snowpuppy/augreality/doc/Team5FinalPresentation.pptx

## ECE 477 Final Presentation Team 05 - Fall 2013

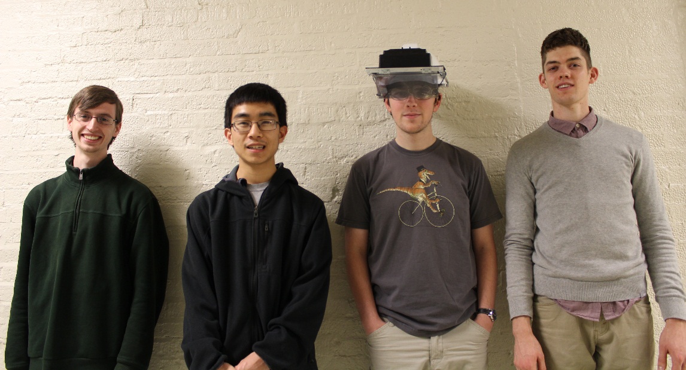
[picture p90: figure]

From left: Thor Smith, Stephen Carlson, Steven Ellis, Alec Green

## Outline

- Project overview
- Block diagram
- Design challenges
- Individual contributions
- Project demonstration
- Questions / discussion

## Project Overview

- Augmented Reality Simulator
  - Play as Pacman in a mobile, outdoor environment.
  - Designed to support other simulations that require an augmented environment and multiple users.
- Contains two primary parts: a headset and a central control unit (CCU)
  - The headset is worn by the user and overlays images of game objects on the user’s view of the environment
  - The CCU remains stationary and communicates information to the headset about simulation logic.

## Slide 4

## Design Challenges

- Packaging
  - Needs to be lightweight and comfortable
  - Stability of IMU mounting
  - Semi-transparent display
- Headset Pi Software
  - 3D rendering
  - SPI communication with µC

## Design Challenges

- Hardware Design
  - PCB needs to fit Raspberry Pi footprint
  - Battery power and power supply
- Headset µC Software
  - XBee communication
  - Sensor filtering
  - SPI communication with Raspberry Pi

## Individual Contributions

- Team Leader - Thor Smith
- Team Member 2 - Alec Green
- Team Member 3 - Stephen Carlson
- Team Member 4 - Steven Ellis

## Team Leader - Thor Smith

- User interface on the Central Control Unit.
- Networking packets sent between the Central Control Unit and the Headset.
- Inter-process Communication between user interface, simulation, and packet program.
- Worked with Steven Ellis on packaging design and construction.
- Organized most team meetings and purchased most parts for project.

## Member 2 - Alec Green

- Google Maps parsing for automatic map generation
  - Image process map tiles
  - GPS location from pixel coordinate
- Packet protocol definition
- IMU sensors
  - Calculate Euler angles from sensor readings
  - Research and design filters
- Compiled Video

## Member 3 - Stephen Carlson

- Design Constraint Analysis
  - Research parts
  - Select candidate based on project requirements
- Schematic and Theory of Operation
  - Power supply design
  - Select pins/ports on microcontroller
- PCB Layout
  - Design for manufacturability
  - Power handling and impedance matching
- Assembly and Soldering

## Member 4 - Steven Ellis

- Graphics
  - Created game 3D models
  - Custom configuration file format
  - OpenGL code
- Raspberry Pi SPI code
  - Integration with graphics
- Packaging
  - Assembly
  - Optics research
  - Model for 3D printed enclosure

## Project Demonstration

1. An ability to render graphics based on the orientation of the user’s head.
2. An ability to render graphics based on the user’s current geospatial location.
3. An ability to monitor and display the battery power level of the headset to the user.
4. An ability to monitor and display the status and quality of the wireless connection to the central control unit.
5. An ability to load headset graphics for a new simulation without re-flashing software on the headset’s microcontroller.

## Questions / Discussion
