snowpuppy/augreality/doc/TCSP9.pptx

## Team 5 environmental impact analysis

Steven Ellis

## Manufacture (very bad)

- Packaging
  - Aluminum, ABS, and acrylic
- Lithium polymer battery
  - LiCoO2 electrode
    - LiFePO4 would be less harmful
- PCB
  - Etching uses either ammonium persulfate
  - Lead solder
    - Switch to lead-free solder
- LCD
  - Sulfur hexafluoride used in manufacture
  - LED backlighting avoids mercury found in CCFL

## Use (not so bad)

- Electricity used to power device
  - Only draws ~5 watts in use
  - ‘Phantom power’ when turned off is tens of microwatts
- Product lifespan
  - Battery lasts ~400 charge cycles
    - LiFePO4 would increase this to ~2000
  - Battery can be replaced without replacing entire unit

## End of life (also pretty bad)

- Packaging
  - Aluminum and plastics can both be recycled
- Lithium polymer battery
  - Nonhazardous waste
  - Can be recycled
- PCB
  - Neither biodegradable nor recyclable
- LCD
  - Neither biodegradable nor recyclable

## Questions?
