snowpuppy/augreality/doc/Team5PCBNarrative.pptx

## PCB Layout Narrative

Team 05 Augmented Reality Project
TCSP #05
Stephen Carlson, Steven Ellis, Alec Stephen Green, Thor Smith

## Abstract

- We propose an augmented reality simulator
  - Allows at least one user to play an electronic game in a mobile, outdoor environment
  - Intended for gaming and other simulations that require an augmented environment
- Contains two primary parts: a headset and a central control unit (CCU)
  - The headset is worn by the user and overlays images of game objects on the user’s view of the environment
  - The CCU remains stationary and communicates information to the headset about simulation logic.

Team 05: Augmented Reality

## Functional Block Diagram


* CCU will not have a PCB

## PSSC Review

- An ability to render graphics based on the orientation of the user’s head.
- An ability to render graphics based on the user’s current geospatial location.
- An ability to monitor and display the battery power level of the headset to the user.
- An ability to monitor and display the status and quality of the wireless connection to the central control unit.
- An ability to load headset graphics for a new simulation without re-flashing software on the headset’s microcontroller.

## Layout Considerations – General

- Advanced Circuits/4PCB specs
  - 5mil trace/5mil space
  - 10mil minimum hole size and 5mil tolerance
- For manufacturability
  - 10mil trace/8mil space
  - 15mil minimum hole size
- No acute angles
- Two layers

## Layout Considerations – MCU

- Oscillator and USB lines match impedance
  - Trace lengths must match
  - No right angles
- Decoupling, oscillator must be adjacent
  - Place some capacitors underneath chip
- Pin locations determine routing success

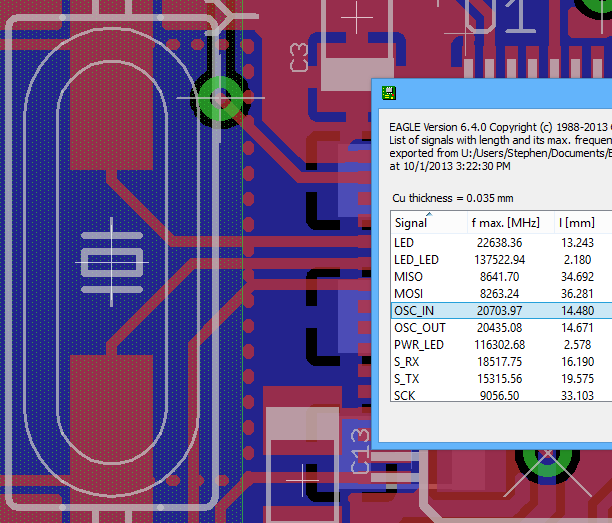
[picture p122: figure]

## Layout Considerations – Power

- Total current could be up to 2A
  - Use low resistance copper pours
  - Multiple large vias for transfer between layers
  - Power from multiple directions (“islands”)
  - Bulk capacitors near regulator, bypass near loads


## Layout Considerations – Other

- Connectors
  - Raspberry PI connector must match motherboard
  - Other connectors must be on edges
- Route I²C, UART, SPI lines together
  - Test points
- Debug LEDs, spare I/O headers
- Place V_ADC regulator near IMU
  - Reduce interference pickup
  - Place XBee far away


## Layout, Full Board

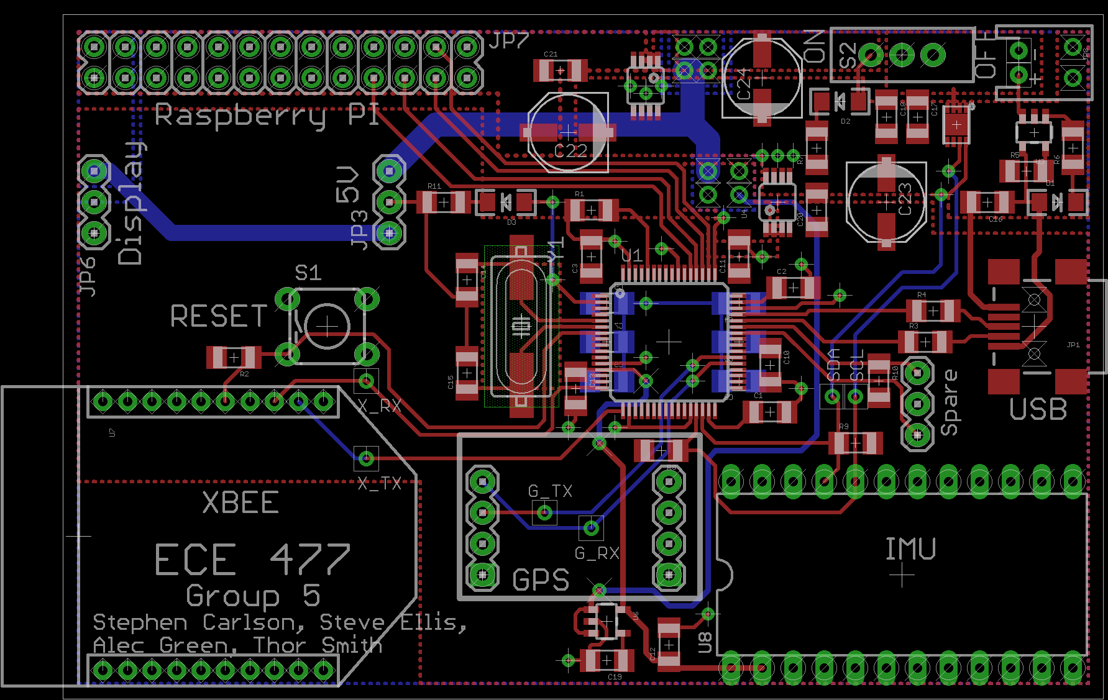
[picture p123: figure]

## Questions

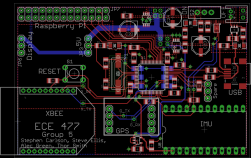
[picture p124: figure]
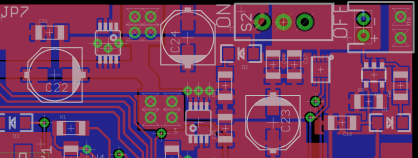
[picture p125: figure]
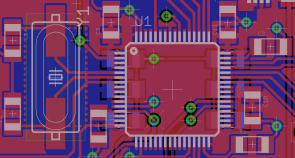
[picture p126: figure]
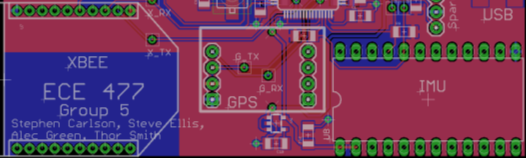
[picture p127: figure]

## Layout, Power Supply

Power Switch

JST Connector

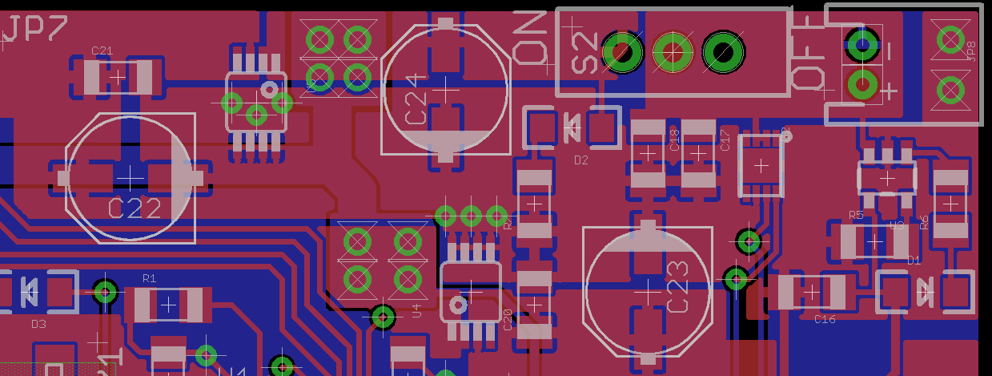
[picture p128: figure]

Core Supply

Fuel Gauge

Power LED

Charger

MCU Supply

Charging LED


## Layout, Microcontroller

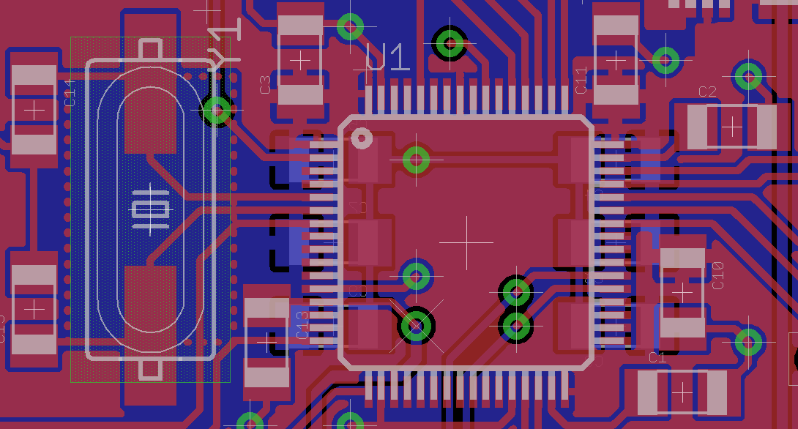
[picture p129: figure]

SPI to
Raspberry PI

8MHz
Oscillator

STM32F4
Microcontroller

To USB
(programming)

To Reset Button

UART to XBee

UART to GPS

I²C to IMU


## Layout, Peripherals

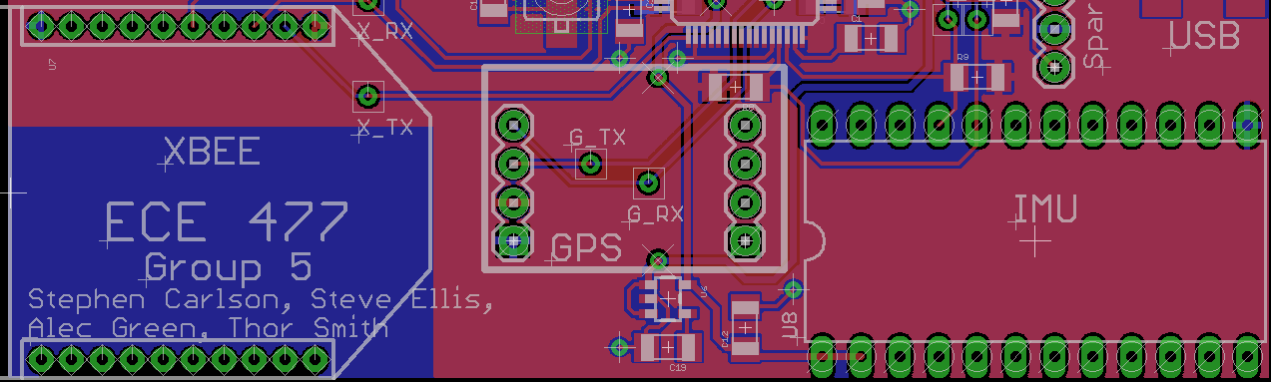
[picture p130: figure]

XBee Pro 900

Venus GPS Breakout

ST 9-DOF IMU Breakout

V_ADC
Supply
