snowpuppy/augreality/doc/FinalSubmission/README - Augmented Reality Simulator.docx

Augmented Reality Final Submission Index File

The Augmented Reality Simulator archive contains the following files, to be reviewed in the order listed.

1. Cornell Cup Final Report : Word document containing final report
2. Graphical Timeline Appendix: Word document containing a visual representation of the timeline
3. Timeline Appendix: Excel spreadsheet containing a listing of dates for the timeline
4. Bill Of Materials Appendix: Excel spreadsheet listing items bought and used for the project
5. First Design Review: PDF file documenting how our presentation was evaluated and comments suggested
6. Second Design Review: Word document explaining main talking points of the design review
7. Phase 1 Senior Design Report: Word document containing the report written for phase 1 of this project
8. Phase 2 Sensor Schematic Appendix: Schematic of phase 2’s sensors and microcontroller system
9. Phase 2 Power Schematic Appendix: Schematic of phase 2’s power supply
10. Phase 2 Sensor PCB Layout Appendix: Printed circuit board (PCB) layout views of phase 2’s sensor and microcontroller PCB
11. Phase 2 Power PCB Layout Appendix: PCB layout views of phase 2’s power supply PCB
12. Phase 1 Schematic Appendix: Schematic of the full system board used for phase 1
13. Phase 1 PCB Layout Appendix: PCB layout views of the full system board used for phase 1
