snowpuppy/augreality/doc/Phase 2 Power PCB Layout.docx

# Layout, Composite

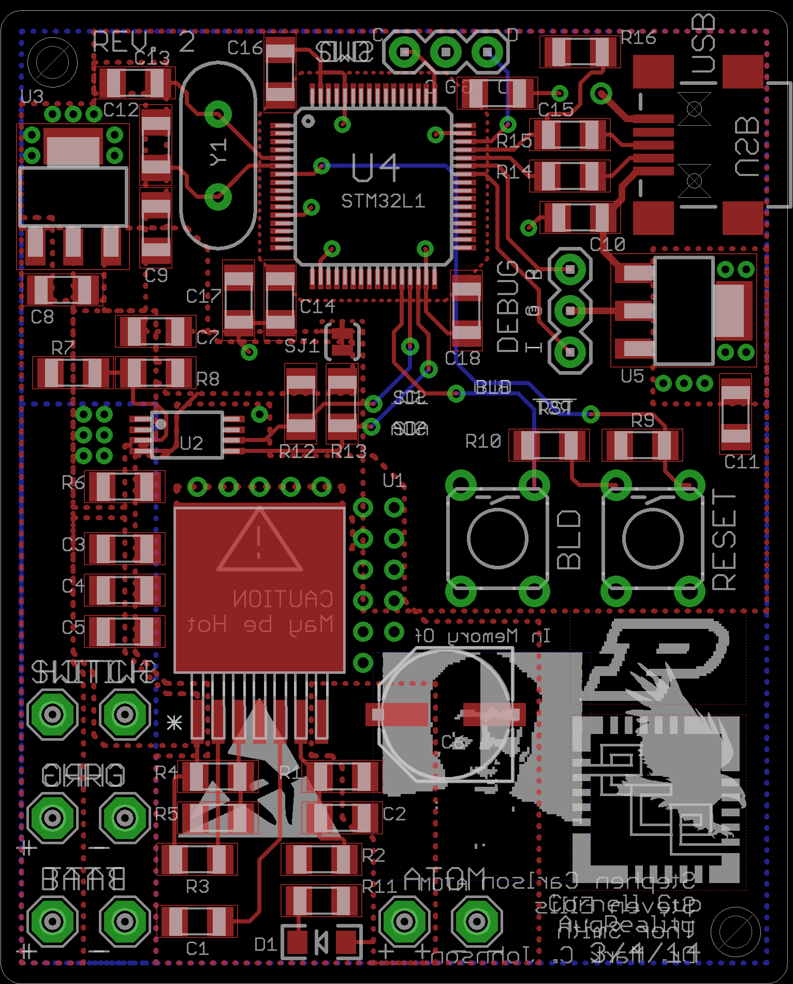
[picture p137: figure]

# Layout, Top Copper

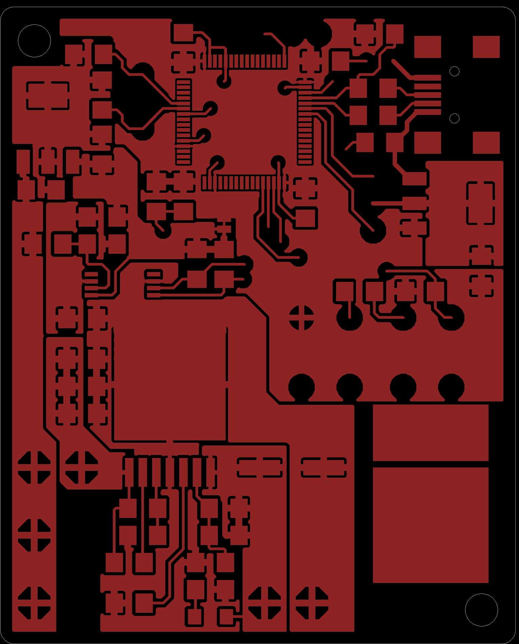
[picture p138: figure]

# Layout, Bottom Copper

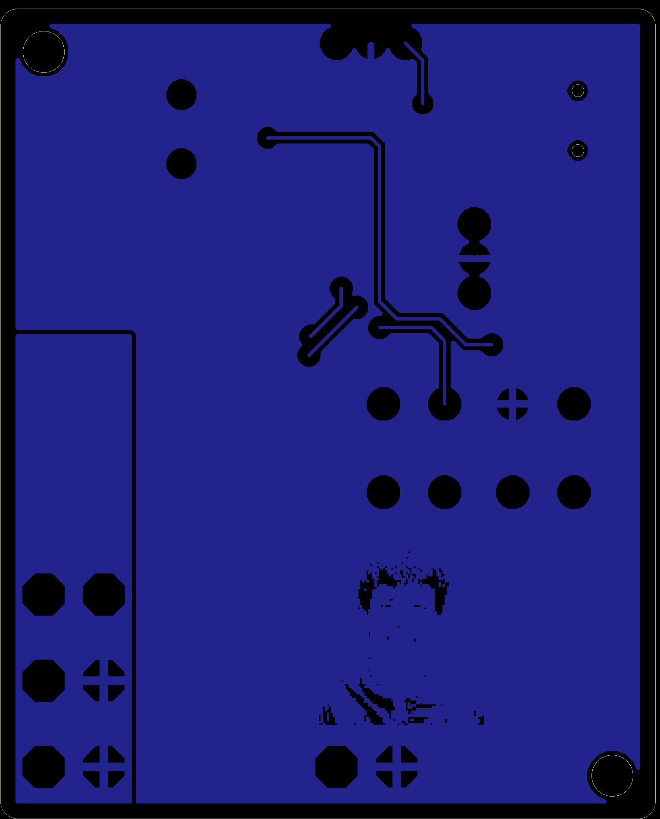
[picture p139: figure]

# Layout, Top Silk Screen

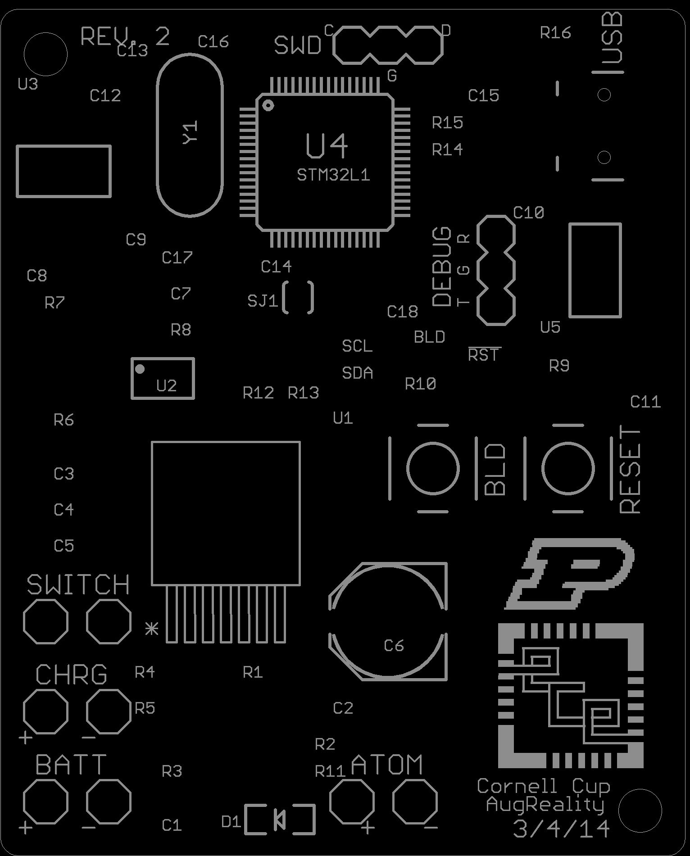
[picture p140: figure]

# Layout, Bottom Silk Screen

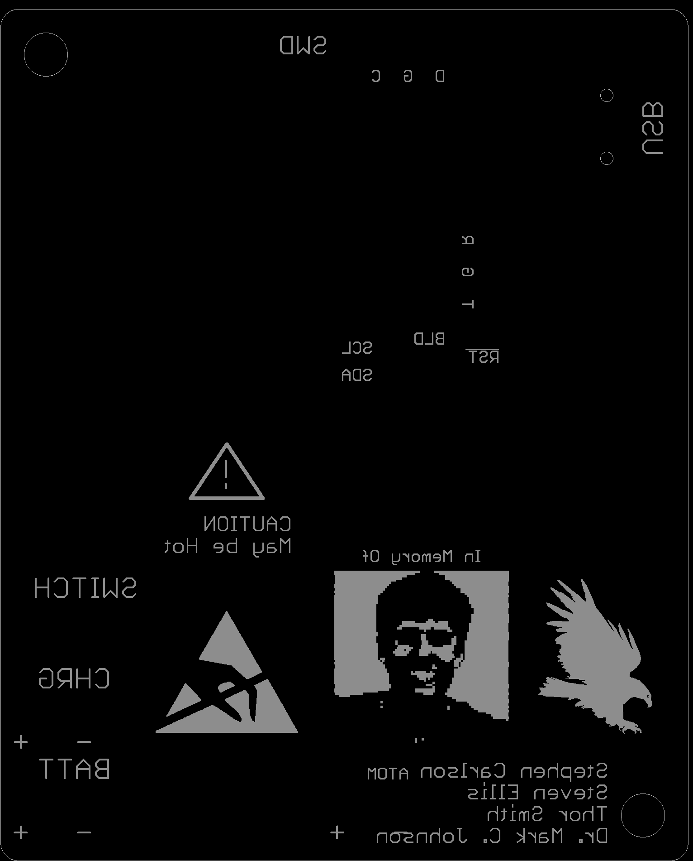
[picture p141: figure]
