snowpuppy/augreality/doc/Phase 2 Sensor PCB Layout.docx

# Layout, Composite

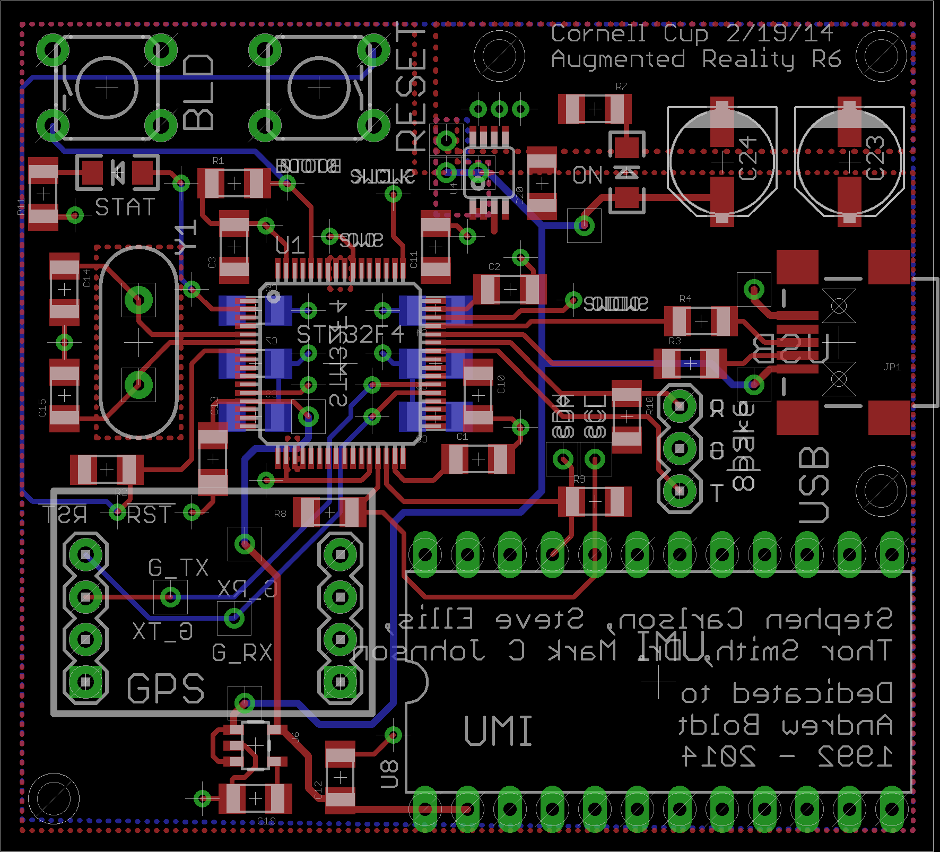
[picture p142: figure]

# Layout, Top Copper

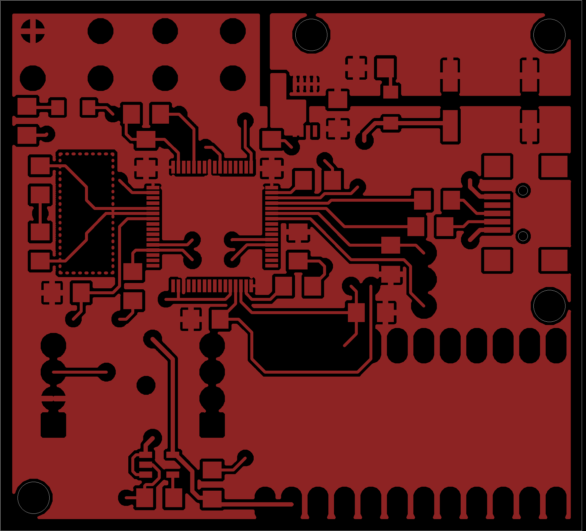
[picture p143: figure]

# Layout, Bottom Copper

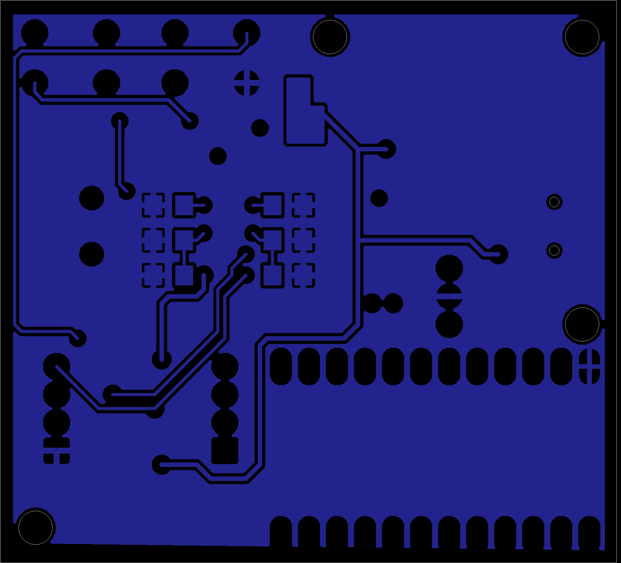
[picture p144: figure]

# Layout, Top Silk Screen

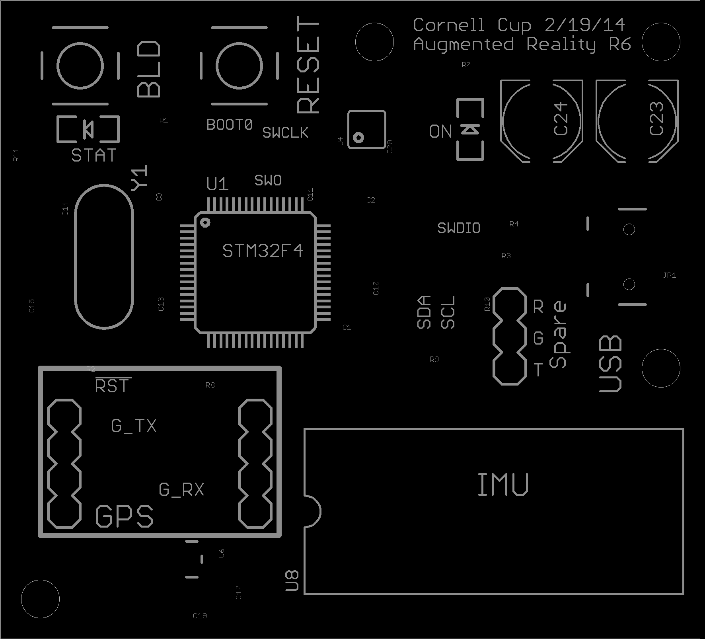
[picture p145: figure]

# Layout, Bottom Silk Screen

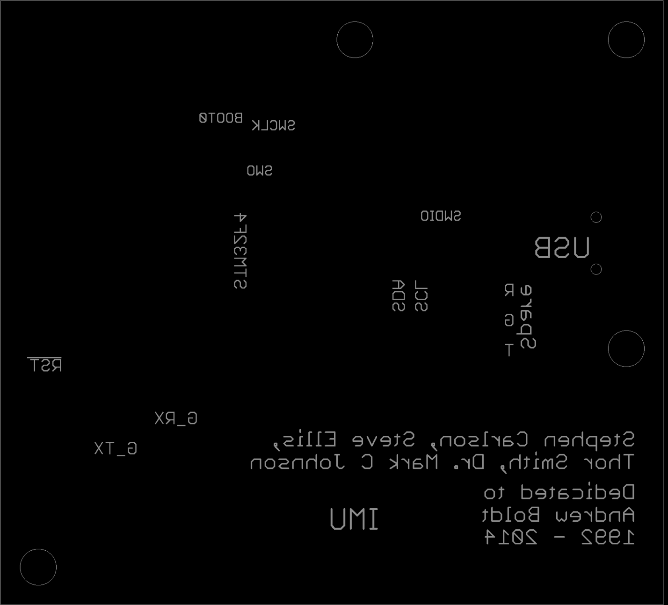
[picture p146: figure]
