snowpuppy/augreality/doc/FinalSubmission/Graphical Timeline Appendix.docx

Graphical Timeline

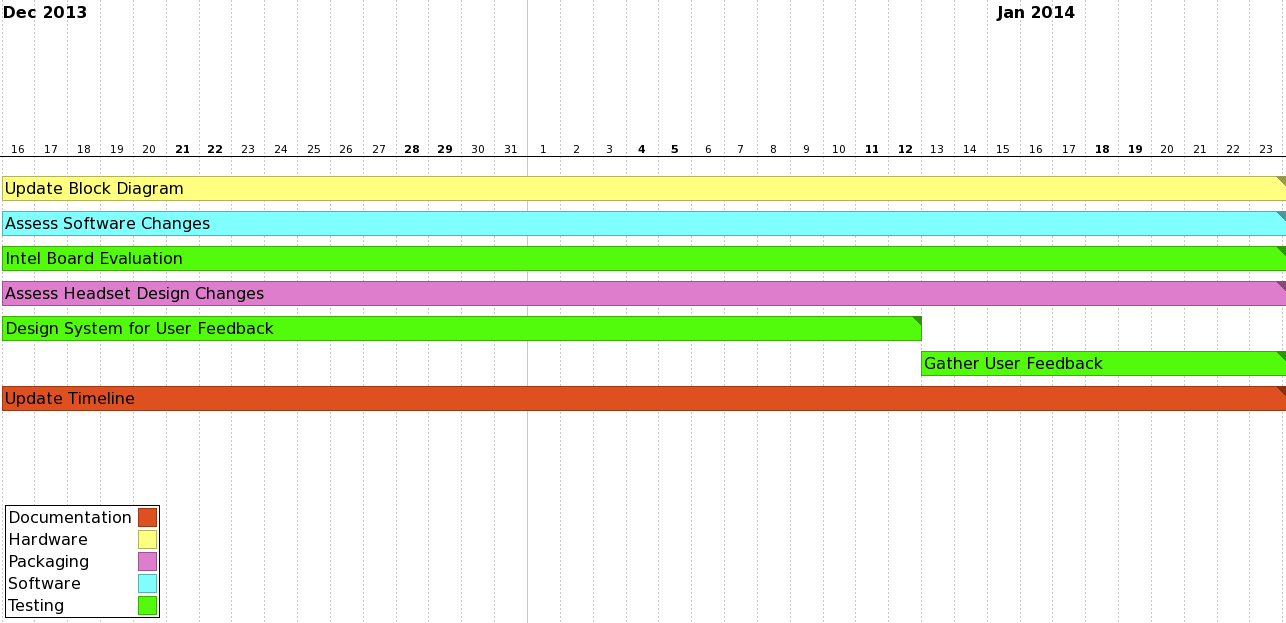
[picture p147: figure]
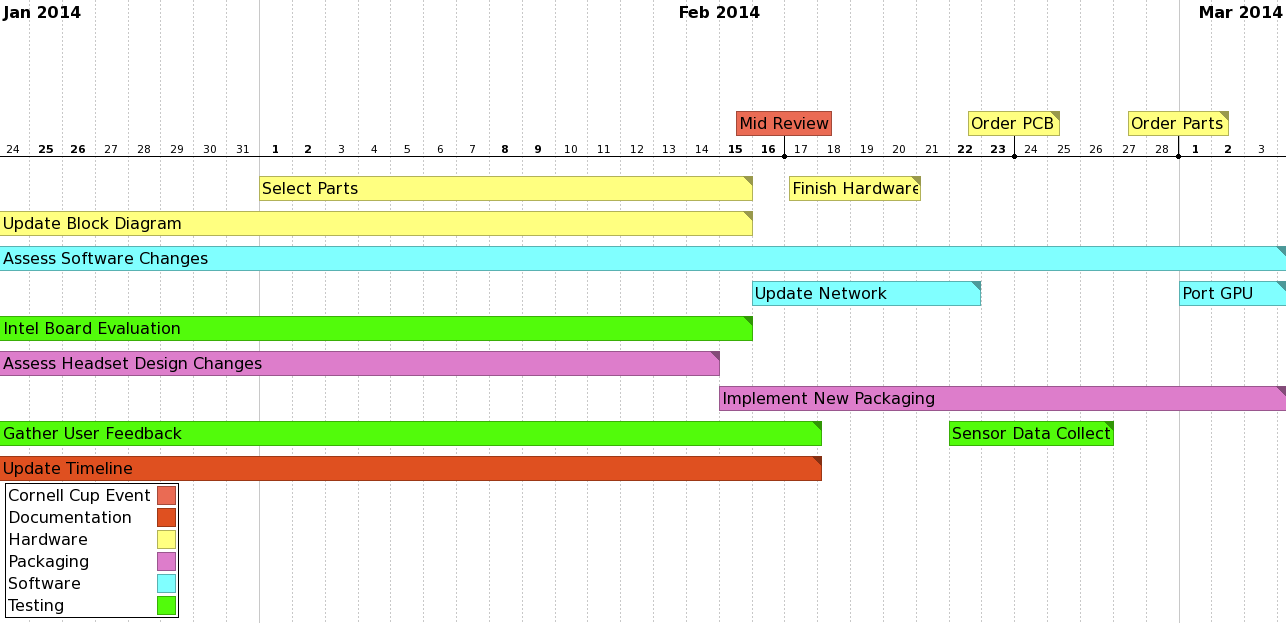
[picture p148: figure]
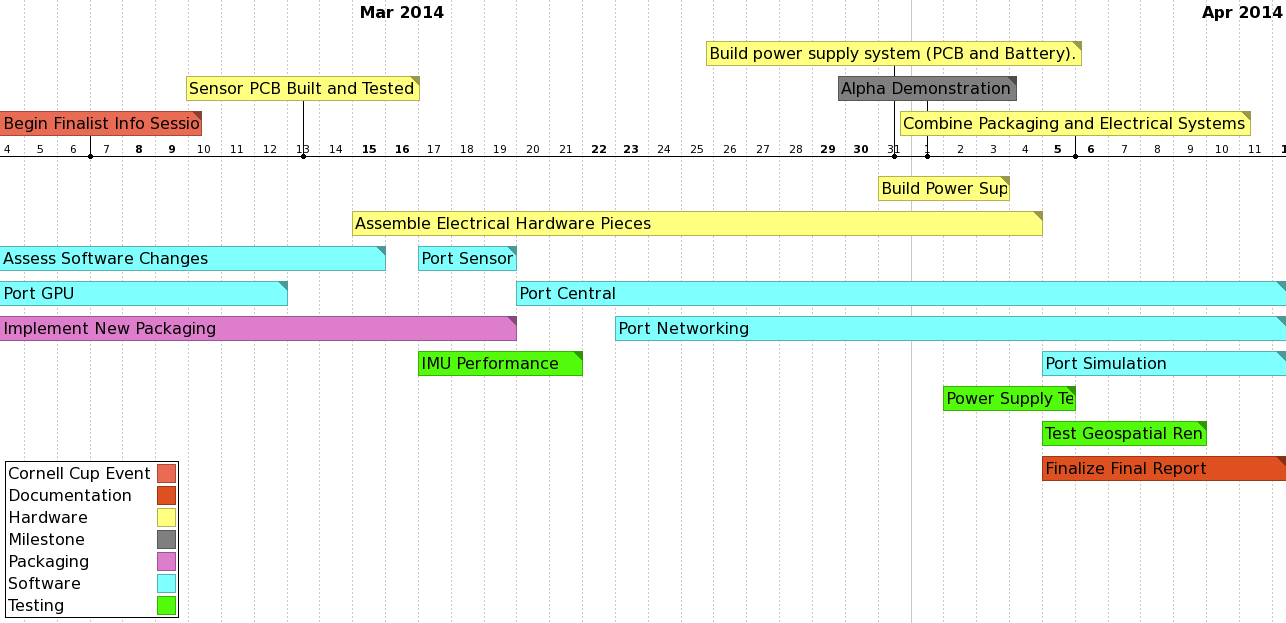
[picture p149: figure]
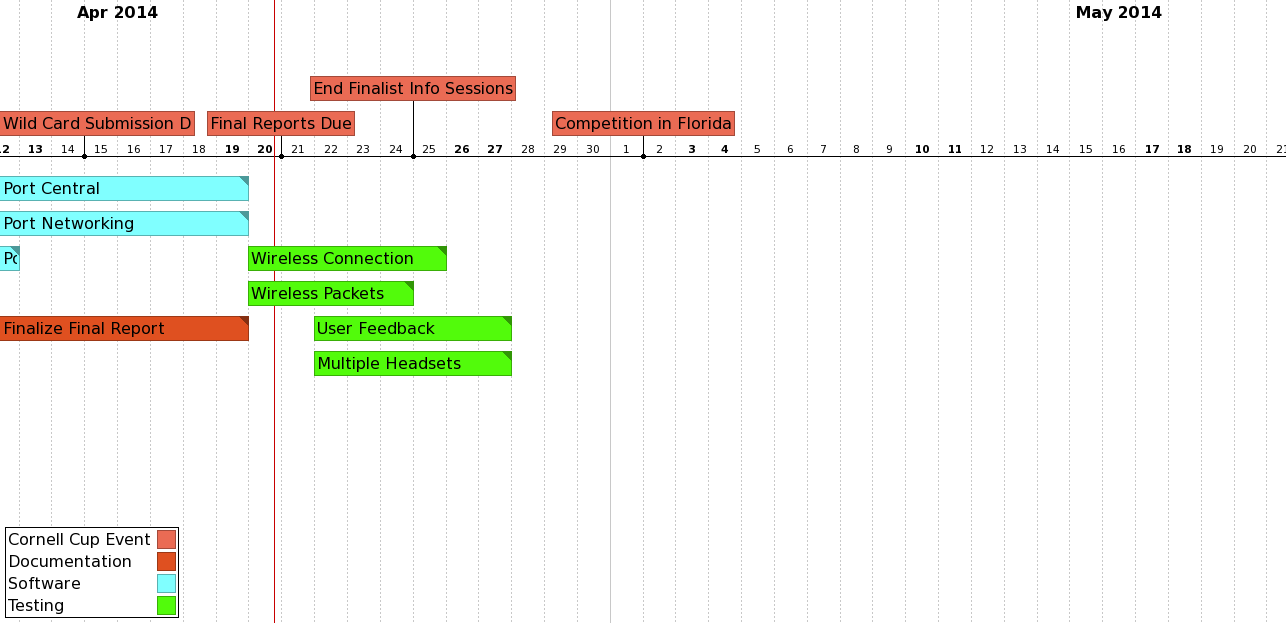
[picture p150: figure]
