snowpuppy/augreality/doc/FinalSubmission/Phase 1 PCB Layout Appendix.pdf

Layout, Composite

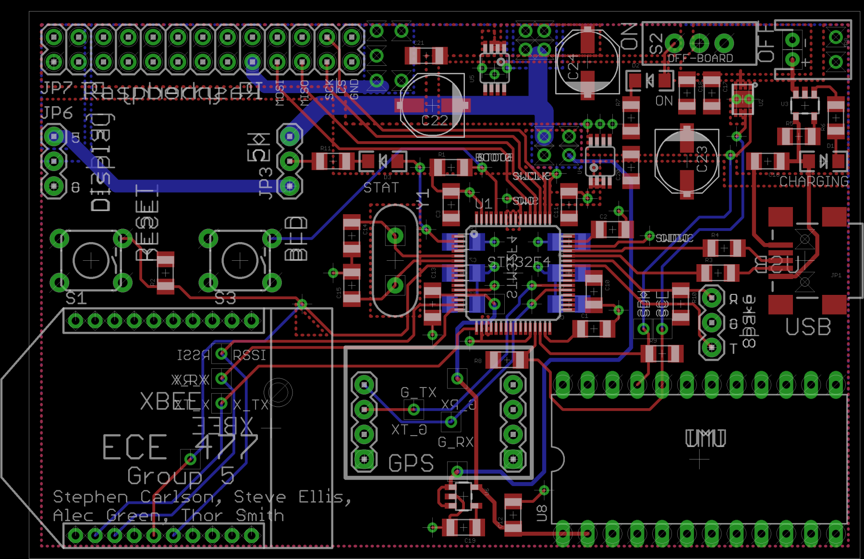
[picture p151: figure]

Layout, Top Copper


Layout, Bottom Copper


Layout, Top Silk Screen


Layout, Bottom Silk Screen
