snowpuppy/augreality/doc/FinalSubmission/Phase 2 Power PCB Layout Appendix.pdf

Layout, Composite


Layout, Top Copper

Layout, Bottom Copper

Layout, Top Silk Screen

Layout, Bottom Silk Screen
