snowpuppy/augreality/doc/Final Report Status.xlsx

Section | Person
Abstract | Everyone
Challenge Definition | Carlson
Customer Value Proposition | Carlson
Changes from Proposal | Carlson
Key Technical Elements | Everyone
Performance Metrics | Ellis
Failure Analysis | Carlson
Timeline | Thor
Timeline changes writeup | Thor
Budget | Thor
Mid-review writeup | Carlson
Process Understanding | Thor
Recomendations and next steps | Thor
Glossary | Ellis
Acknowledgements | Carlson
Survey Responses | Ellis
Testing instructions | Carlson
Assembly instructions | Ellis
Technical Documentation | Everyone
Red = no progress
Yellow = some progress
Green = completed
