snowpuppy/augreality/headset/src/sensor_micro_src/src/i2c.c

/*
 * Cornell Cup 2014 - Augmented Reality Simulator
 *
 * Stephen Carlson
 * Steven Ellis
 * Thor Smith
 * Dr. Mark C. Johnson
 *
 * i2c.c - I2C implementation
 */

#include "main.h"
#include <stm32f4xx_i2c.h>

// I2C statuses
#define I2C_READ_BIT ((uint8_t)0x01)
#define I2C_STATUS_ERR ((uint8_t)0x01)
#define I2C_STATUS_RESTART ((uint8_t)0x02)
#define I2C_STATUS_NOSTOP ((uint8_t)0x04)

// I2C status to use
typedef struct {
	// Up or down?
	volatile uint8_t status;
	// Target I2C address
	volatile uint8_t address;
	// Byte count left
	volatile uint16_t count;
	// Byte buffer to use
	volatile uint8_t *buffer;
} I2CStatus_TypeDef;

volatile I2CStatus_TypeDef i2cState;

// _i2cDisableInt - Common I2C end routine to disable interrupts
static inline void _i2cDisableInt() {
	I2C2->CR2 &= ~(I2C_CR2_ITEVTEN | I2C_CR2_ITBUFEN);
}

// _i2cEnableInt - Common I2C start routine to enable interrupts
static inline void _i2cEnableInt() {
	I2C2->CR2 |= I2C_CR2_ITEVTEN | I2C_CR2_ITBUFEN;
}

/**
 * Initializes the I2C peripheral. The STM32F4 address is set to 0x10.
 */
void i2cInit() {
	GPIO_InitTypeDef gs;
	I2C_InitTypeDef is;
	// Clocks on
	RCC_APB1PeriphClockCmd(RCC_APB1Periph_I2C2, ENABLE);
	// GPIOs set up
	gs.GPIO_Mode = GPIO_Mode_AF;
	gs.GPIO_OType = GPIO_OType_OD;
	gs.GPIO_PuPd = GPIO_PuPd_NOPULL;
	gs.GPIO_Speed = GPIO_Speed_50MHz;
	gs.GPIO_Pin = GPIO_Pin_10 | GPIO_Pin_11;
	GPIO_Init(GPIOB, &gs);
	GPIO_PinAFConfig(GPIOB, GPIO_PinSource10, GPIO_AF_I2C2);
	GPIO_PinAFConfig(GPIOB, GPIO_PinSource11, GPIO_AF_I2C2);
	// Reset I2C
	I2C2->CR1 = I2C_CR1_SWRST;
	for (uint32_t delay = 0; delay < 128; delay++) asm volatile("");
	I2C2->CR1 = 0;
	// Configure I2C
	is.I2C_ClockSpeed = 400000;
	is.I2C_Mode = I2C_Mode_I2C;
	is.I2C_DutyCycle = I2C_DutyCycle_2;
	is.I2C_OwnAddress1 = 0x10;
	is.I2C_Ack = I2C_Ack_Disable;
	is.I2C_AcknowledgedAddress = I2C_AcknowledgedAddress_7bit;
	I2C_Init(I2C2, &is);
	// Turn I2C on
	I2C_Cmd(I2C2, ENABLE);
	// Turn on error interrupt (event interrupt turned on when needed)
	I2C_ITConfig(I2C2, I2C_IT_ERR, ENABLE);
	i2cState.status = 0;
	// IRQs on
	NVIC_EnableIRQ(I2C2_ER_IRQn);
	NVIC_EnableIRQ(I2C2_EV_IRQn);
	NVIC_SetPriority(I2C2_ER_IRQn, 1);
	NVIC_SetPriority(I2C2_EV_IRQn, 1);
}

// Reads the specified number of data bytes from the specified address
static bool _i2cRead(uint8_t addr, uint8_t *data, uint32_t count) {
	volatile I2CStatus_TypeDef *state = &i2cState;
	__disable_irq();
	{
		// Set the I2C direction to reception, set LSB to receive properly
		state->address = (addr << 1) | I2C_READ_BIT;
		// Set up buffers
		state->buffer = data;
		state->count = count;
		// Send START condition
		state->status &= ~I2C_STATUS_ERR;
		I2C2->CR1 |= I2C_CR1_ACK | I2C_CR1_START;
		state->status = 0;
	}
	_i2cEnableInt();
	__enable_irq();
	// Wait until START is reset (transmission begins)
	const unsigned long timeout = millis() + 5UL;
	do {
		// Wait until BUSY flag is reset (until a STOP is generated)
		__WFI();
		// Error occurred?
		if (state->status & I2C_STATUS_ERR)
			return false;
		// I2C should never take this long
		if (millis() >= timeout)
			return false;
	} while (i2cState.count > 0);
	// Work around for I2C locks
	for (uint32_t i = 10000; i; i--) asm volatile("nop\n\t");
	return true;
}

// Writes data to the I2C interface, observing the NOSTOP flag for repeated-start generation
static bool _i2cWrite(uint8_t addr, uint8_t *data, uint32_t count) {
	uint8_t status;
	volatile I2CStatus_TypeDef *state = &i2cState;
	__disable_irq();
	{
		// Set the I2C direction to transmission, clear LSB to transmit properly
		state->address = addr << 1;
		// Set up buffers
		state->buffer = data;
		state->count = count;
		// Send START condition
		state->status &= ~(I2C_STATUS_ERR | I2C_STATUS_RESTART);
		I2C2->CR1 |= I2C_CR1_START | I2C_CR1_ACK;
	}
	_i2cEnableInt();
	__enable_irq();
	// Wait until START is reset (transmission begins)
	const unsigned long timeout = millis() + 5UL;
	do {
		// Wait until BUSY flag is reset (until a STOP is generated) or repeated-start bit set
		__WFI();
		status = state->status;
		// Error occurred?
		if (status & I2C_STATUS_ERR)
			return false;
		// I2C should never take this long
		if (millis() >= timeout)
			return false;
	} while (i2cState.count > 0);
	// Work around for I2C locks
	for (uint32_t i = 10000; i; i--) asm volatile("nop\n\t");
	return true;
}

/**
 * Reads the specified number of data bytes from the specified address.
 *
 * @param addr the target address to read
 * @param data the buffer into which data will be placed
 * @param count the number of bytes to read
 * @return whether the operation completed successfully
 */
bool i2cRead(uint8_t addr, uint8_t *data, uint32_t count) {
	return _i2cRead(addr, data, count);
}

/**
 * Reads the specified number of data bytes from a given register on the specified address,
 * using the I2C "Repeated Start" convention.
 *
 * @param addr the target address to read
 * @param reg the register address on the target to read
 * @param data the buffer into which data will be placed
 * @param count the number of bytes to read
 * @return whether the operation completed successfully
 */
bool i2cReadRegister(uint8_t addr, uint8_t reg, uint8_t *value, uint32_t count) {
	i2cState.status |= I2C_STATUS_NOSTOP;
	// Write out the location we want and read in data
	return _i2cWrite(addr, &reg, 1) && _i2cRead(addr, value, count);
}

/**
 * Writes the specified number of data bytes to the specified address.
 *
 * @param addr the target address to write
 * @param data the buffer where data is stored
 * @param count the number of bytes to write
 * @return whether the operation completed successfully
 */
bool i2cWrite(uint8_t addr, uint8_t *data, uint32_t count) {
	i2cState.status &= ~I2C_STATUS_NOSTOP;
	return _i2cWrite(addr, data, count);
}

/**
 * Writes a data byte to the specified register on the specified address.
 *
 * @param addr the target address to write
 * @param reg the register address on the target to write
 * @param value the byte to write
 * @return whether the operation completed successfully
 */
bool i2cWriteRegister(uint8_t addr, uint8_t reg, uint8_t value) {
	uint8_t data[2];
	// Write register, value
	data[0] = reg;
	data[1] = value;
	// Write information
	return i2cWrite(addr, data, 2);
}

// I2C2 event interrupt
void __attribute__ (( interrupt("IRQ") )) I2C2_EV_IRQHandler() {
	uint16_t sr1 = I2C2->SR1;
	volatile I2CStatus_TypeDef *state = &i2cState;
	I2C2->SR2;
	if (sr1 & I2C_SR1_SB)
		// If SB = 1, START sent (EV5)
		I2C2->DR = state->address;
	else if (sr1 & I2C_SR1_ADDR) {
		// If ADDR = 1, address sent (EV6)
		uint8_t count = state->count;
		// Write the first data when transmitting (LSB clear)
		if (!(state->address & I2C_READ_BIT)) {
			// Write the first data in the data register
			I2C2->DR = *((state->buffer)++);
			count--;
			state->count = count;
			// If no further data, disable buffer interrupt so as not to have a TXE interrupt
			if (count == 0)
				I2C2->CR2 &= ~I2C_CR2_ITBUFEN;
		} else if (count == 1) {
			// EV6_1, used for single byte reception. Disable ACK and program STOP
			uint16_t cr = I2C2->CR1;
			// No ACK, send STOP
			cr = (cr & ~I2C_CR1_ACK) | I2C_CR1_STOP;
			I2C2->CR1 = cr;
		}
	} else if (sr1 & I2C_SR1_TXE) {
		uint8_t count = state->count;
		// TXE set, transmit data
		if (sr1 & I2C_SR1_BTF) {
			uint8_t status = state->status;
			// EV8_2, both BTF and TXE are set
			if (status & I2C_STATUS_NOSTOP)
				// Prepare for repeated START bit
				state->status = (status & ~I2C_STATUS_NOSTOP) | I2C_STATUS_RESTART;
			else
				// Send STOP
				I2C2->CR1 |= I2C_CR1_STOP;
			// Disable event interrupt to avoid second BTF interrupt
			_i2cDisableInt();
		} else if (count > 0) {
			// Write data
			I2C2->DR = *((state->buffer)++);
			count--;
			state->count = count;
			// If no data left, avoid last TXE interrupt
			if (count == 0)
				I2C2->CR2 &= ~I2C_CR2_ITBUFEN;
		}
	} else if (sr1 & I2C_SR1_RXNE) {
		uint8_t count = state->count;
		// RXNE set, read in data
		*((state->buffer)++) = I2C2->DR;
		count--;
		state->count = count;
		// If one byte left, disable ACK and send STOP (EV7_1)
		if (count == 1)
			// No ACK, send STOP
			I2C2->CR1 = (I2C2->CR1 & ~I2C_CR1_ACK) | I2C_CR1_STOP;
		else if (count == 0)
			// All done
			_i2cDisableInt();
	}
}

// I2C2 error interrupt
void __attribute__ (( interrupt("IRQ") )) I2C2_ER_IRQHandler() {
	uint16_t cr, flags = I2C2->SR1;
	// Store interrupt flags, then clear them
	I2C2->SR1 = flags & ~(I2C_SR1_ARLO | I2C_SR1_BERR | I2C_SR1_OVR | I2C_SR1_AF);
	cr = I2C2->CR1;
	// Recover from arbitration lost and bus error via resetting I2C
	if (flags & (I2C_SR1_ARLO | I2C_SR1_BERR | I2C_SR1_OVR)) {
		// Software reset the I2C peripheral
		I2C2->CR1 = cr | I2C_CR1_SWRST;
		// This delay required for I2C to acknowledge the request
		for (uint32_t delay = 0; delay < 128; delay++) asm volatile("");
		// Clear software reset
		I2C2->CR1 = cr;
	} else
		// Send STOP bit
		I2C2->CR1 = cr | I2C_CR1_STOP;
	// Let SW know to break out of wait state
	i2cState.status |= I2C_STATUS_ERR;
	// Disable future interrupts
	_i2cDisableInt();
}
