snowpuppy/augreality/headset/test/IMU_Filter/main.h

#ifndef MAIN_H_
#define MAIN_H_

#include "arm_math.h"
#include "stm32f4xx.h"
#include "stm32f4xx_rcc.h"
#include "stm32f4_discovery.h"
#include "i2c.h"

extern volatile unsigned long sysTime;

#endif
