snowpuppy/augreality/headset/test/GPSParser/include/main.h

/*
 * main.h - Header file for global functions
 * 
 * Any experienced C or C++ programmer knows the importance of header files. For those who
 * do not, a header file allows multiple files to reference functions in other files without
 * necessarily having to see the code (and therefore causing a multiple definition).
 */

#ifndef MAIN_H_

// This prevents multiple inclusion, which isn't bad for this file but is good practice
#define MAIN_H_

#include <API.h>

// Allow usage of this file in C++ programs
#ifdef __cplusplus
extern "C" {
#endif

// A function prototype looks exactly like its declaration, but with a semicolon instead of
// actual code. If a function does not match a prototype, compile errors will occur.

// main - runs user code in threaded mode
int main();

// End C++ export structure
#ifdef __cplusplus
}
#endif

#endif
